cheeseprince/gmc-obd-releases/screenshots/page0_day_focus3.png

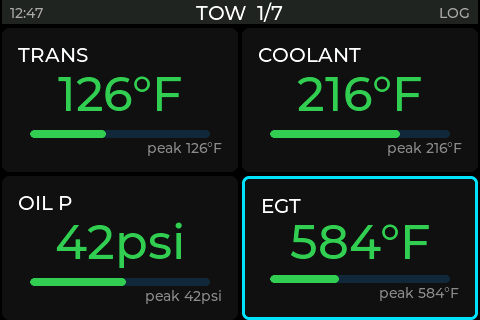
screenshots/page0_day_focus3.png
